danindudesilva/nbiot-ideaboard-v2/enclosure/enclosure.PNG

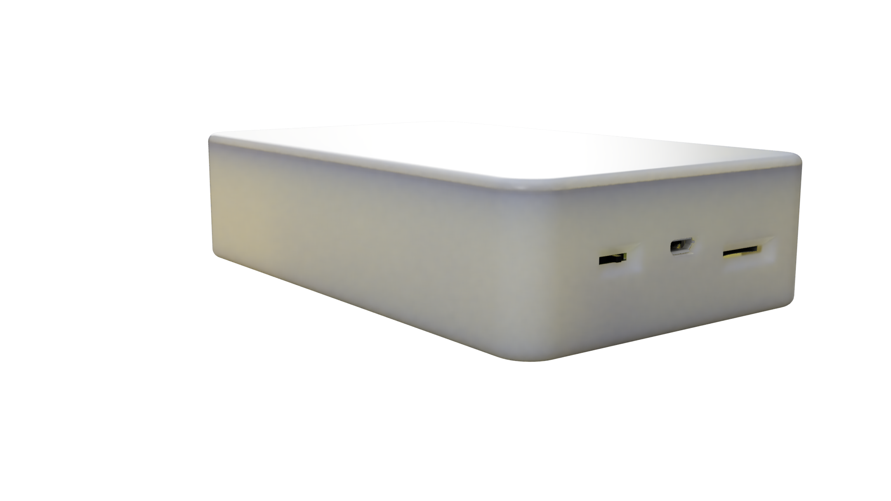
enclosure/enclosure.PNG
