danindudesilva/nbiot-ideaboard-v2/enclosure/enlcosure-2.png

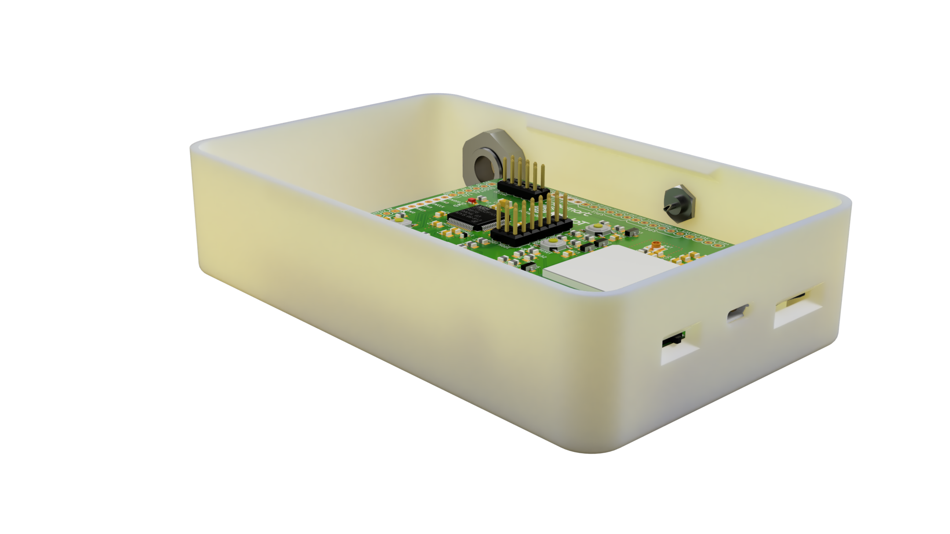
enclosure/enlcosure-2.png
