danindudesilva/nbiot-ideaboard-v2/enclosure/enlcosure-4.png

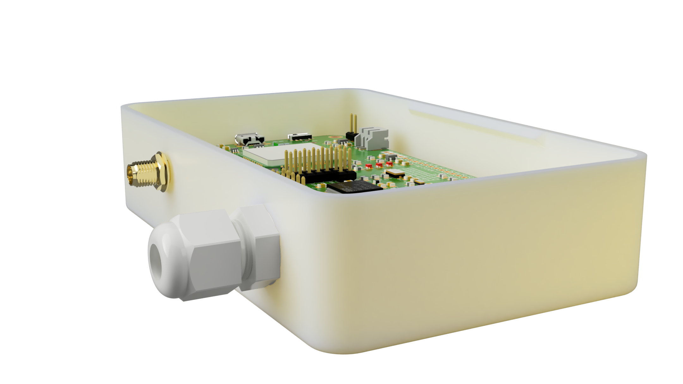
enclosure/enlcosure-4.png
