danindudesilva/nbiot-ideaboard-v2/enclosure/enlcosure-5.png

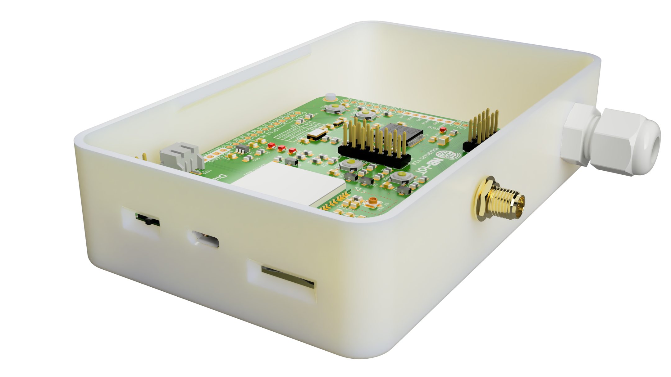
enclosure/enlcosure-5.png
