danindudesilva/nbiot-ideaboard-v2/enclosure/enlcosure-6.png

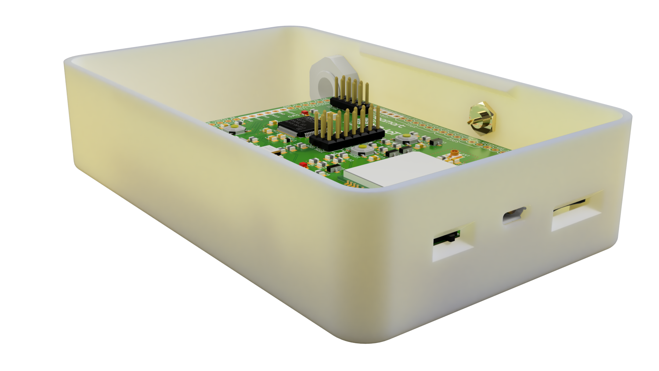
enclosure/enlcosure-6.png
