danindudesilva/nbiot-ideaboard-v2/enclosure/enlcosure-7.png

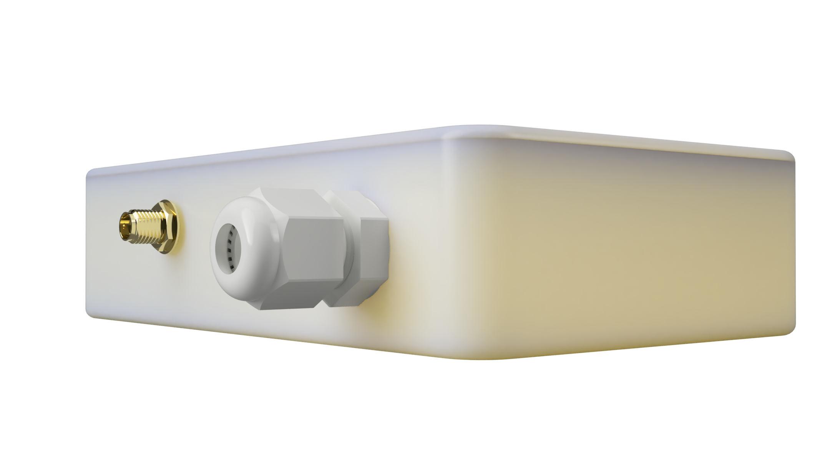
enclosure/enlcosure-7.png
