danindudesilva/nbiot-ideaboard-v2/enclosure/enlcosure-8.png

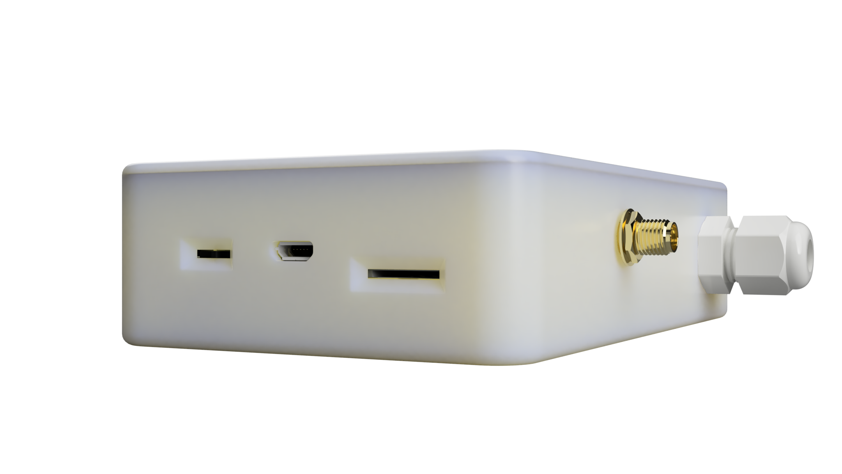
enclosure/enlcosure-8.png
