danindudesilva/nbiot-ideaboard-v2/enclosure/enlcosure-9.png

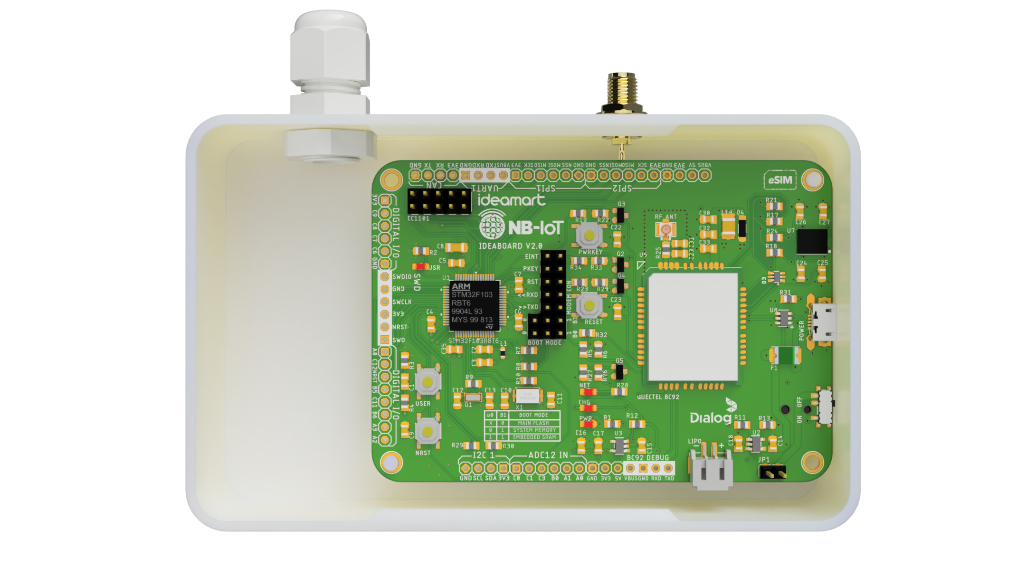
enclosure/enlcosure-9.png
