danindudesilva/nbiot-ideaboard-v2/Images/NB-IoT-ideaboard-v2.0-3D.png

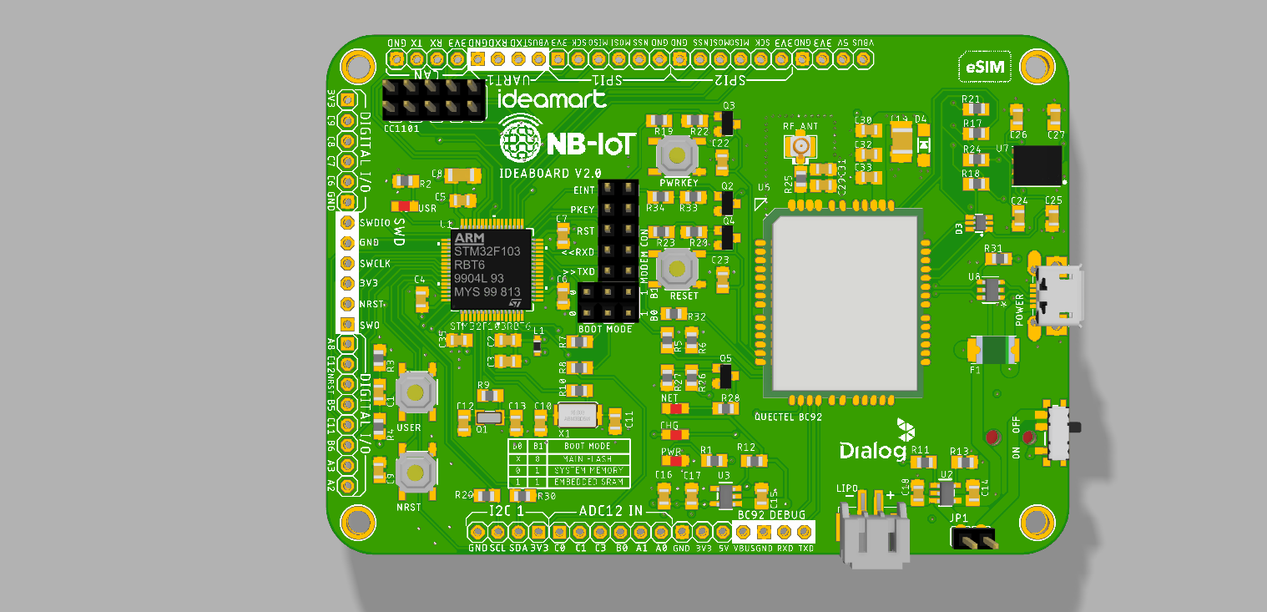
Images/NB-IoT-ideaboard-v2.0-3D.png
