danindudesilva/nbiot-ideaboard-v2/Images/NB-IoT-ideaboard-v2.0-BOTTOM.png

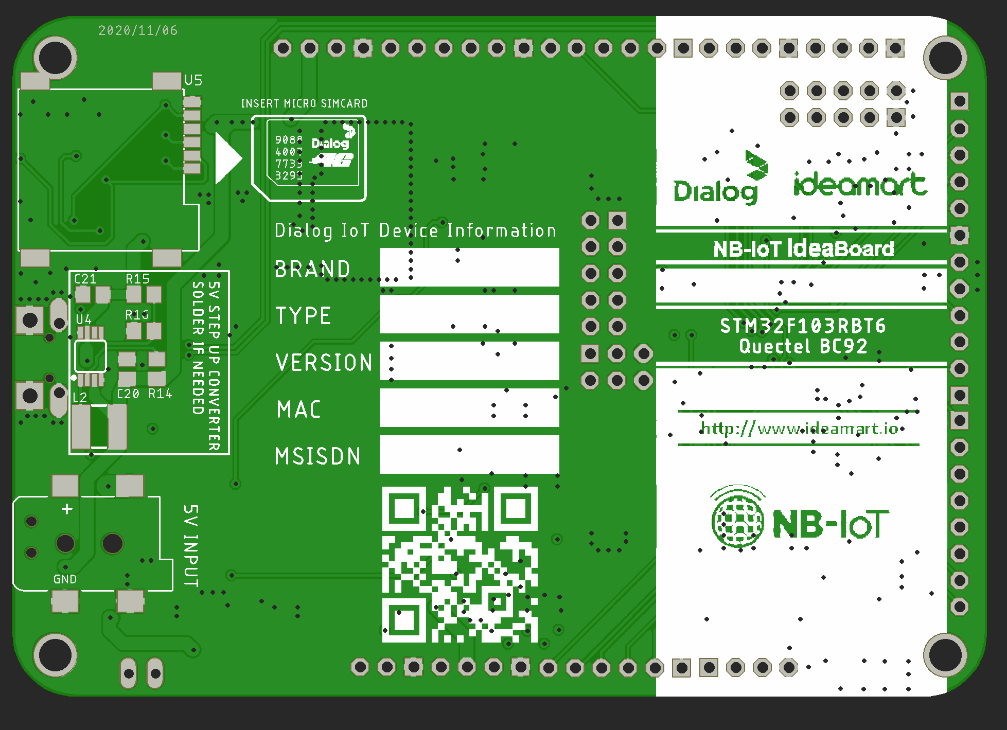
Images/NB-IoT-ideaboard-v2.0-BOTTOM.png
