danindudesilva/nbiot-ideaboard-v2/3D models/parts/dc-jack-smd.step

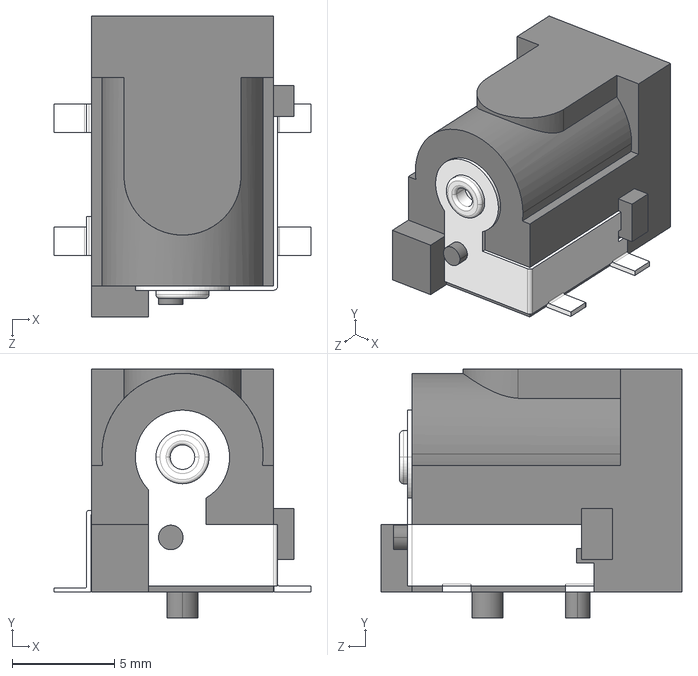
[picture p38: CAD file, 2020-11-13]
3D models/parts/dc-jack-smd.step
12.6 x 12.2 x 14.7 mm
