danindudesilva/nbiot-ideaboard-v2/3D models/parts/sot-23.step

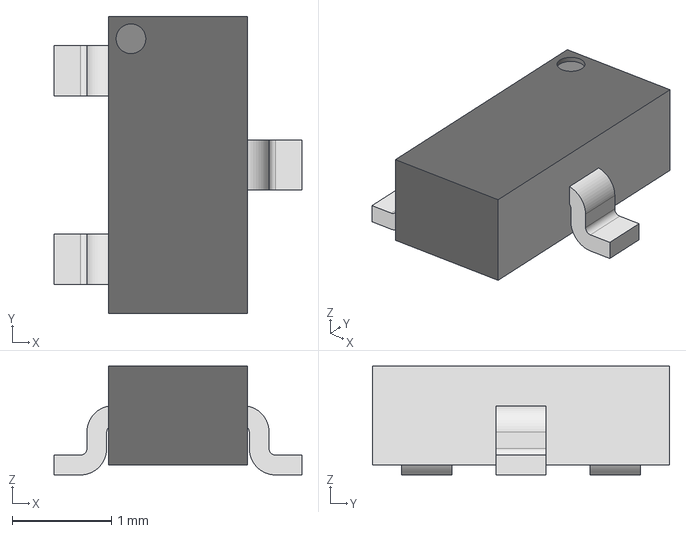
[picture p39: CAD file, 2020-11-13]
3D models/parts/sot-23.step
2.50 x 3.00 x 1.10 mm
