danindudesilva/nbiot-ideaboard-v2/3D models/parts/SOT23-6.step

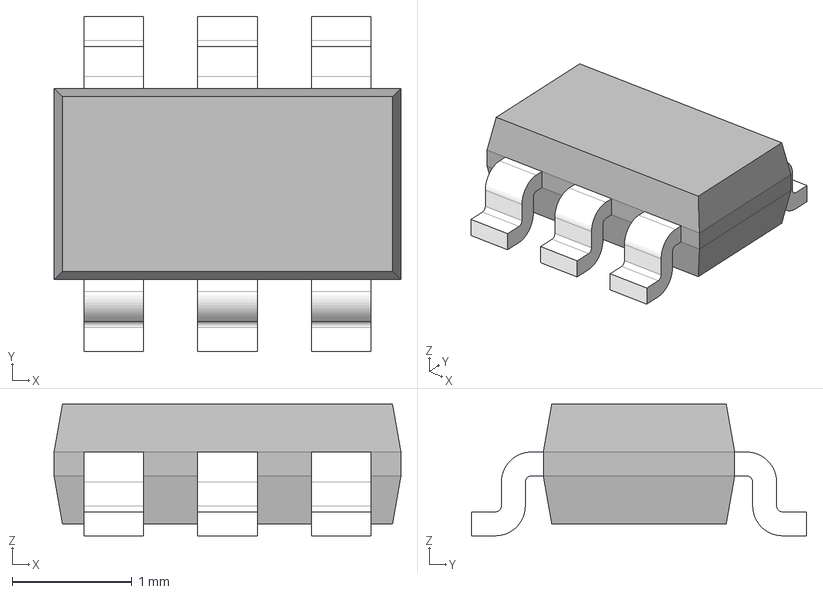
[picture p40: CAD file, 2020-11-13]
3D models/parts/SOT23-6.step
2.90 x 2.80 x 1.10 mm
