danindudesilva/nbiot-ideaboard-v2/3D models/parts/0603LP.step

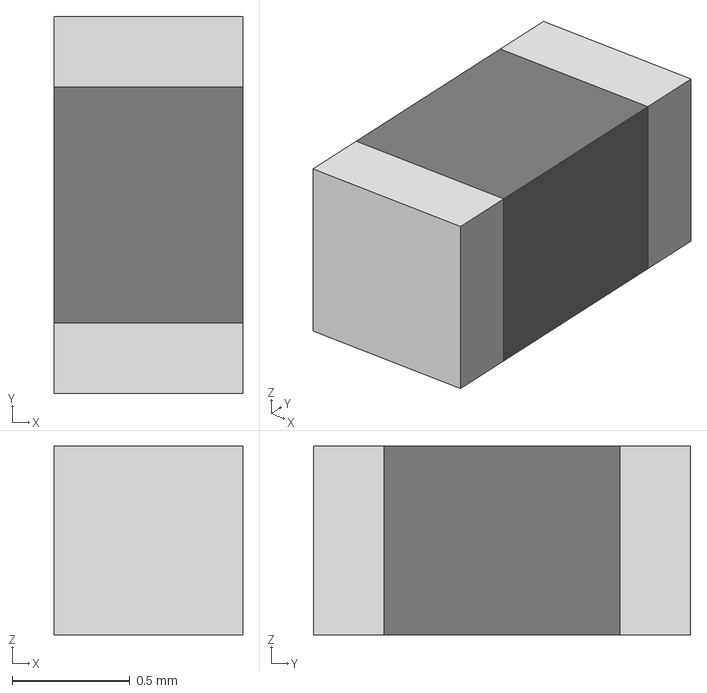
[picture p41: CAD file, 2020-11-13]
3D models/parts/0603LP.step
0.8 x 1.60 x 0.8 mm
Ferrite
Contact x 2
