danindudesilva/nbiot-ideaboard-v2/3D models/parts/crystal-3215.step

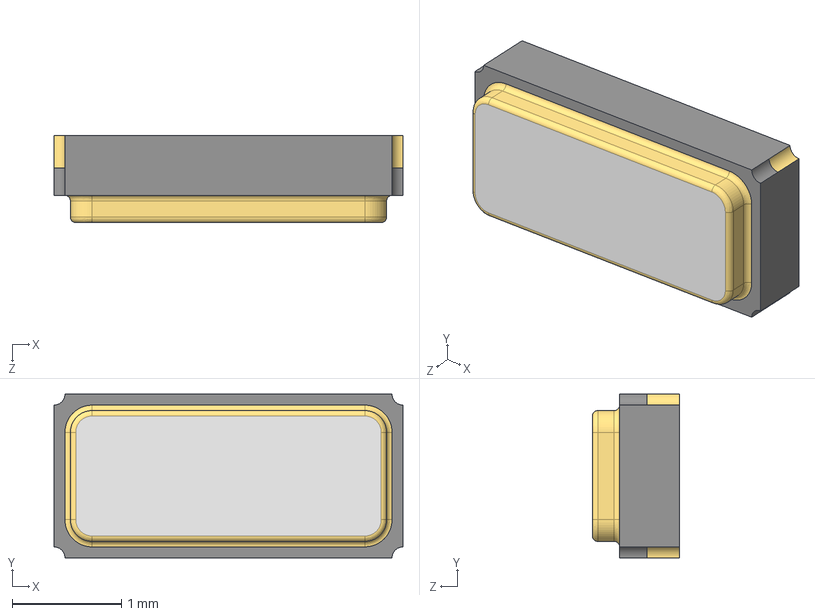
[picture p42: CAD file, 2020-11-13]
3D models/parts/crystal-3215.step
3.20 x 1.50 x 0.8 mm
