danindudesilva/nbiot-ideaboard-v2/3D models/parts/SOT23-5.step

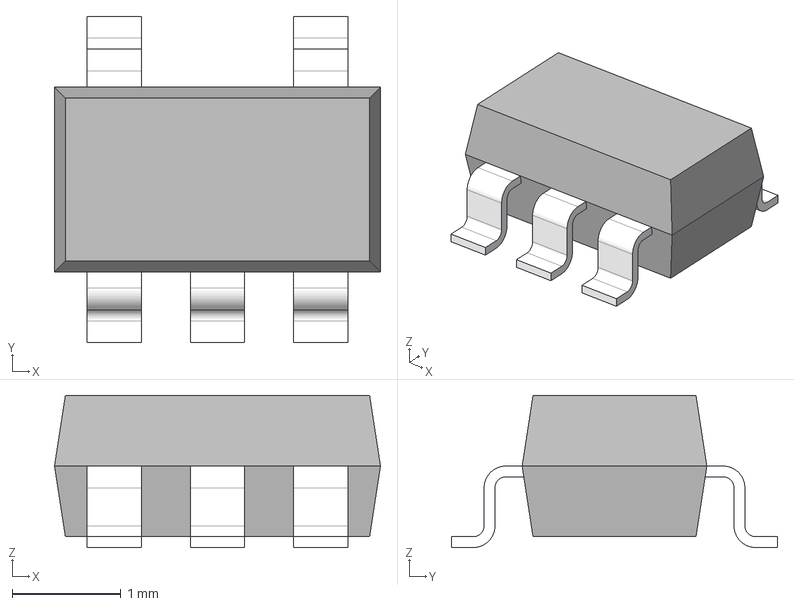
[picture p43: CAD file, 2020-11-13]
3D models/parts/SOT23-5.step
3.00 x 3.00 x 1.40 mm
