danindudesilva/nbiot-ideaboard-v2/3D models/parts/Inductor_0603.step

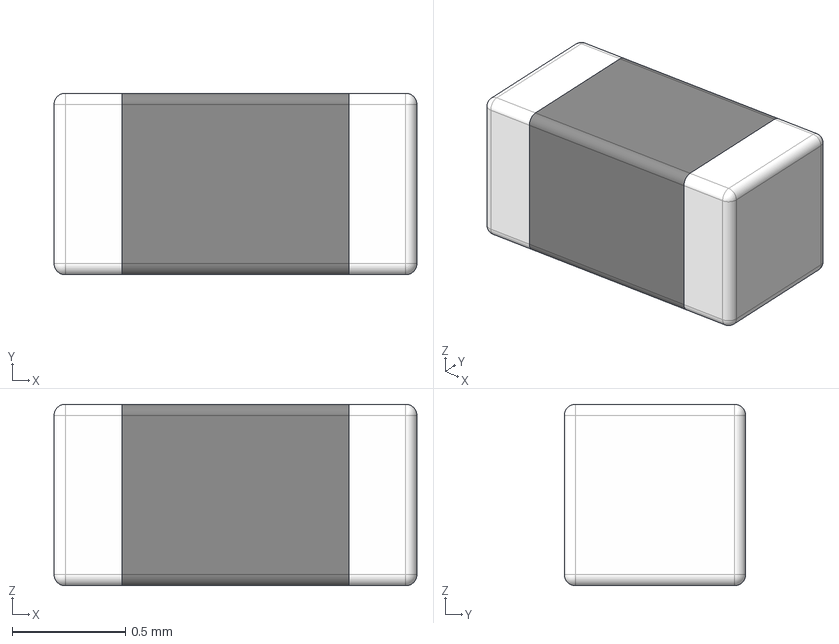
[picture p44: CAD file, 2020-11-13]
3D models/parts/Inductor_0603.step
1.60 x 0.8 x 0.8 mm
Gehäuse
Kontaktfläche x 2
