danindudesilva/nbiot-ideaboard-v2/3D models/parts/spst-slide-switch.step

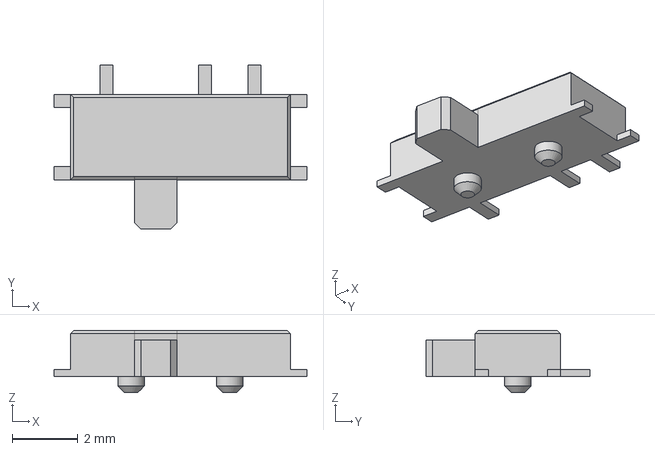
[picture p45: CAD file, 2020-11-13]
3D models/parts/spst-slide-switch.step
7.70 x 5.00 x 1.90 mm
