danindudesilva/nbiot-ideaboard-v2/3D models/parts/Crystal-5032-16.step

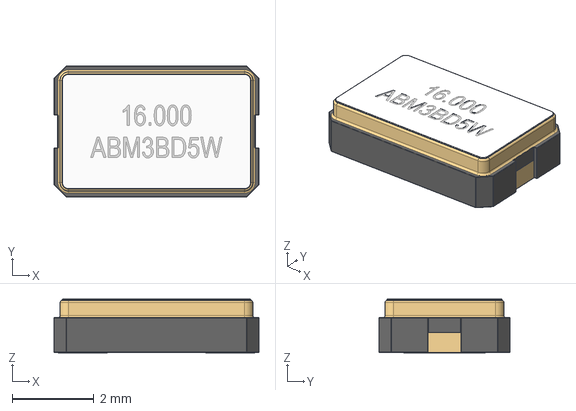
[picture p46: CAD file, 2020-11-13]
3D models/parts/Crystal-5032-16.step
5.00 x 3.20 x 1.31 mm
