danindudesilva/nbiot-ideaboard-v2/3D models/parts/MSOP8.step

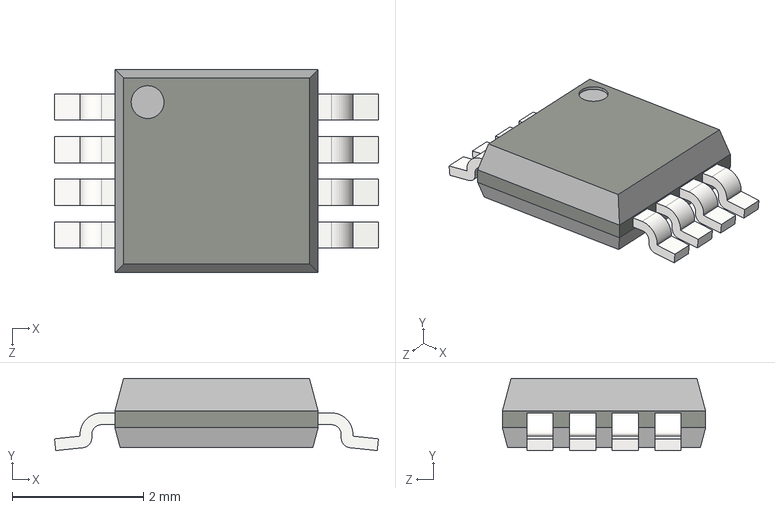
[picture p47: CAD file, 2020-11-13]
3D models/parts/MSOP8.step
4.94 x 1.10 x 3.10 mm
