danindudesilva/nbiot-ideaboard-v2/3D models/parts/BC92.step

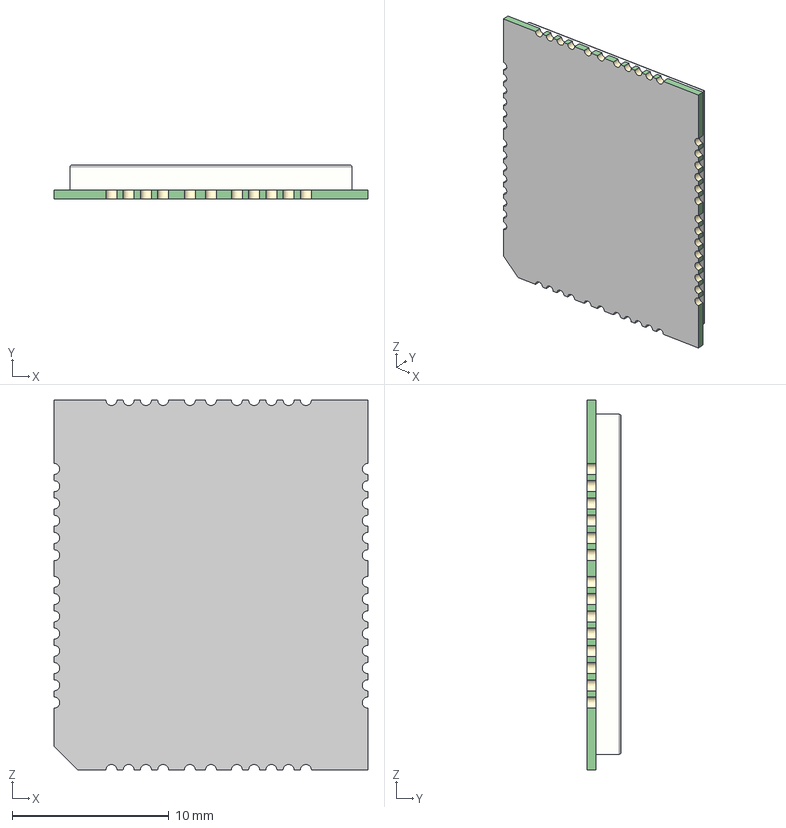
[picture p48: CAD file, 2020-11-13]
3D models/parts/BC92.step
20.0 x 2.20 x 23.6 mm
