danindudesilva/nbiot-ideaboard-v2/3D models/parts/2x5-male.step

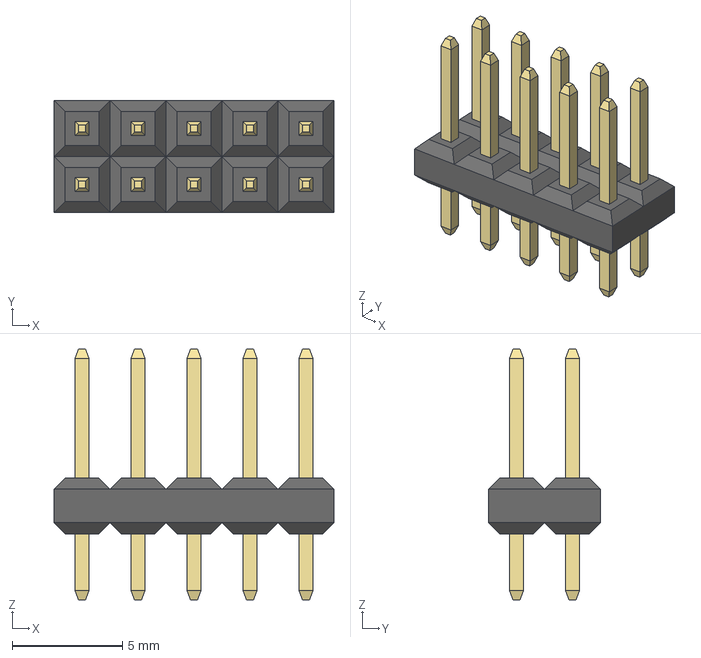
[picture p50: CAD file, 2020-11-13]
3D models/parts/2x5-male.step
12.7 x 5.08 x 11.4 mm
