danindudesilva/nbiot-ideaboard-v2/3D models/parts/micro-usb-female.step

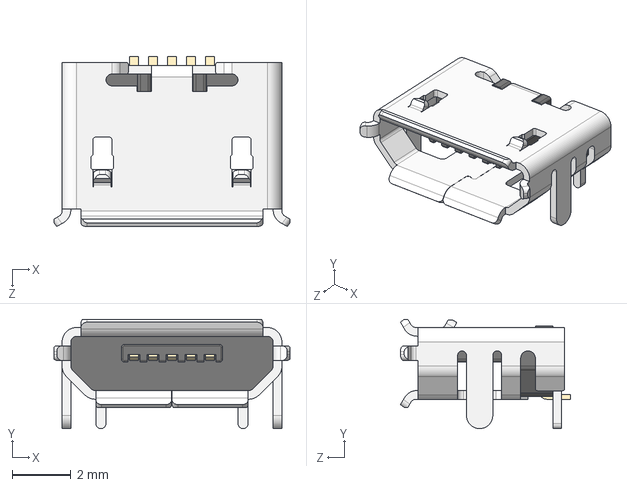
[picture p51: CAD file, 2020-11-13]
3D models/parts/micro-usb-female.step
8.05 x 3.73 x 5.80 mm
