danindudesilva/nbiot-ideaboard-v2/3D models/parts/CHIP-LED0805.step

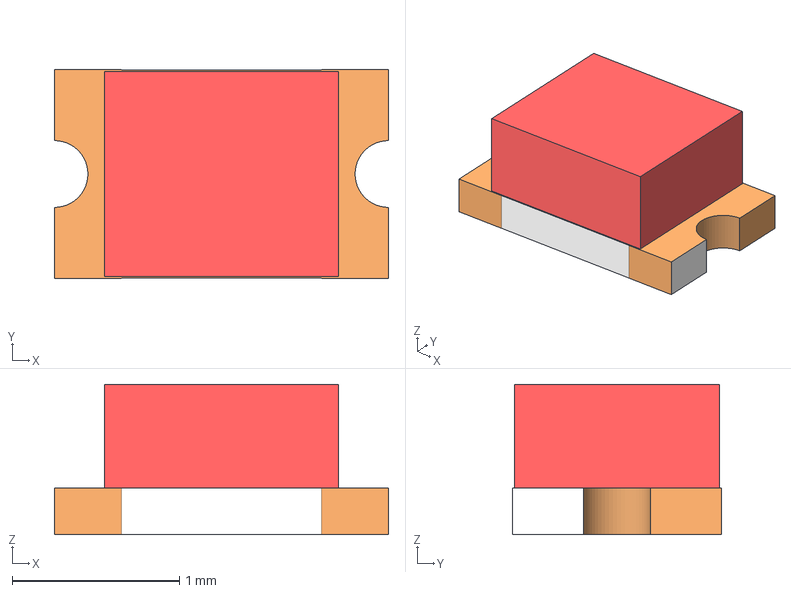
[picture p52: CAD file, 2020-11-13]
3D models/parts/CHIP-LED0805.step
2.00 x 1.25 x 0.9 mm
