danindudesilva/nbiot-ideaboard-v2/3D models/parts/ufl.step

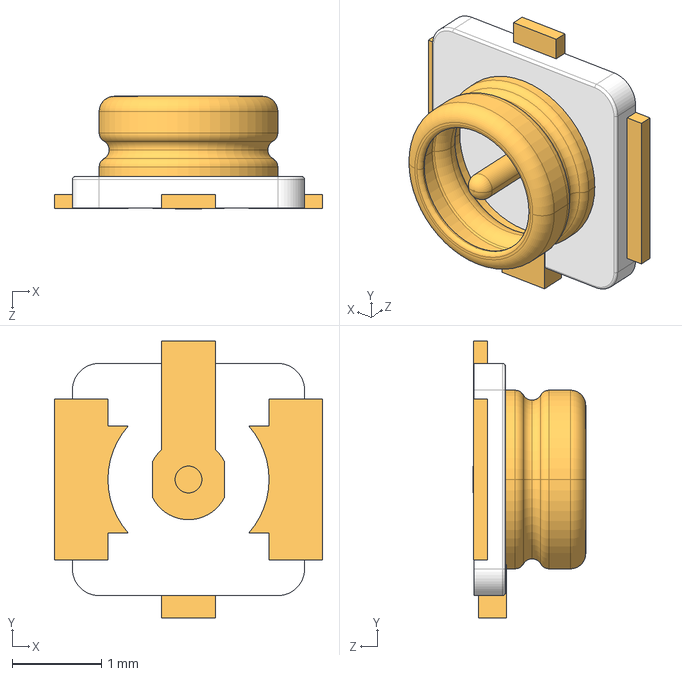
[picture p53: CAD file, 2020-11-13]
3D models/parts/ufl.step
3.00 x 3.10 x 1.26 mm
