danindudesilva/nbiot-ideaboard-v2/3D models/parts/MFF2-esim.step

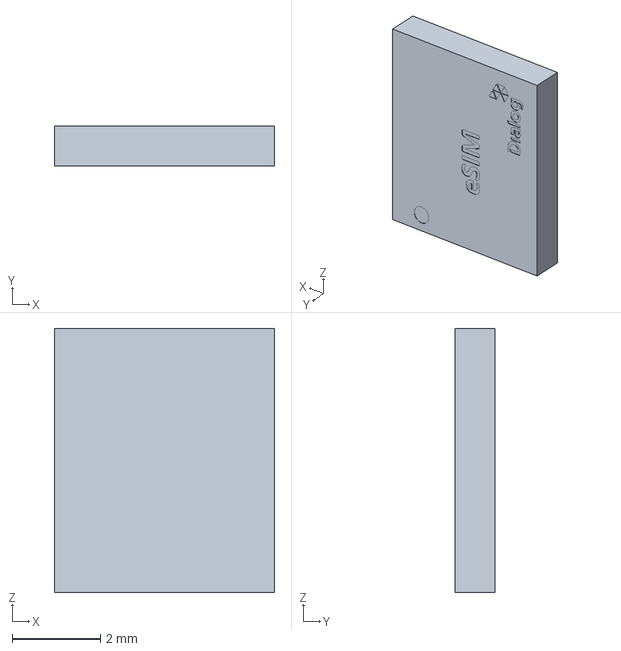
[picture p54: CAD file, 2020-11-13]
3D models/parts/MFF2-esim.step
5.00 x 0.9 x 6.00 mm
