danindudesilva/nbiot-ideaboard-v2/3D models/parts/jst-2-pin.step

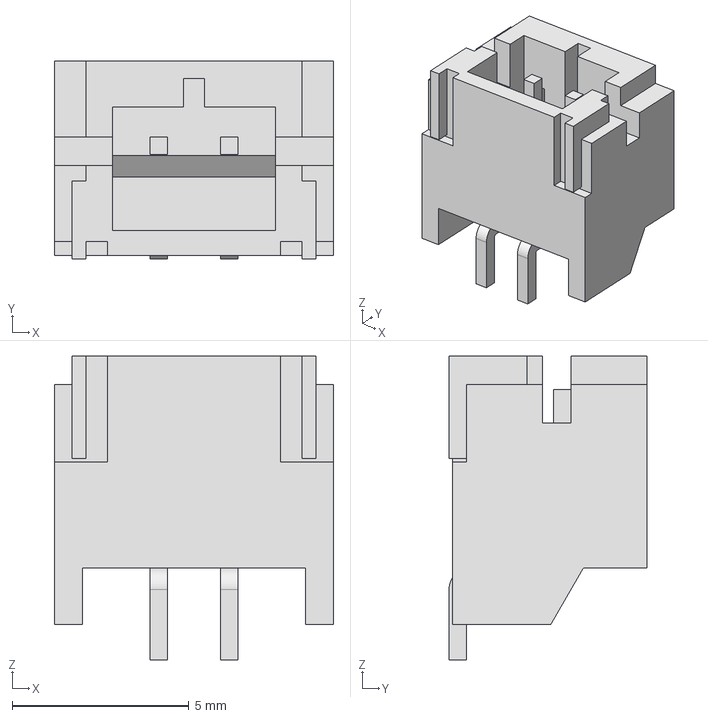
[picture p55: CAD file, 2020-11-13]
3D models/parts/jst-2-pin.step
7.90 x 5.60 x 8.60 mm
